harikrishnan-kp/Non_Mechanical_Anemometer/Images/Exp_setup1.jpg

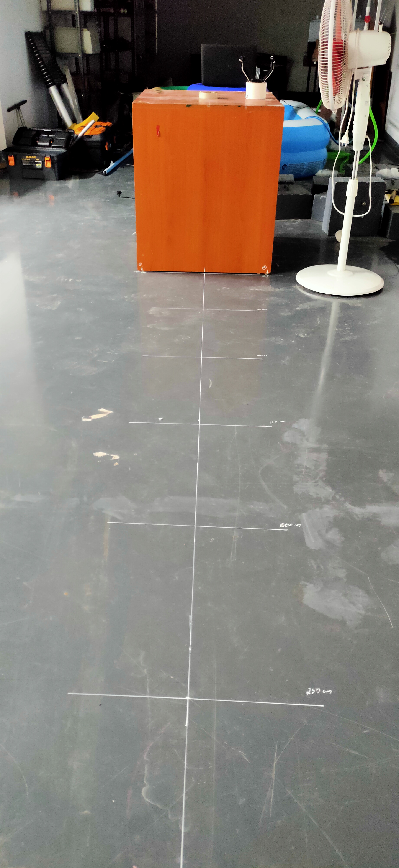
Images/Exp_setup1.jpg
