harikrishnan-kp/Non_Mechanical_Anemometer/Images/anemometer_indoor_testsetup.jpg

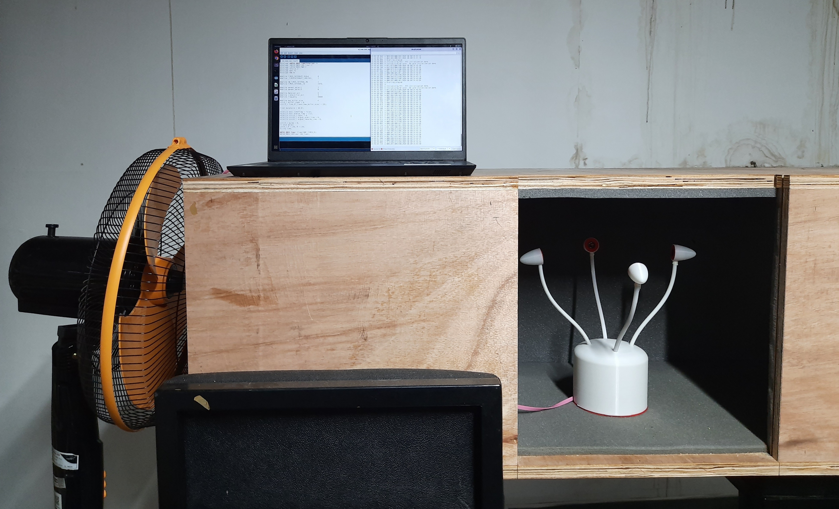
Images/anemometer_indoor_testsetup.jpg
