harikrishnan-kp/Non_Mechanical_Anemometer/Images/anemometer_result.png

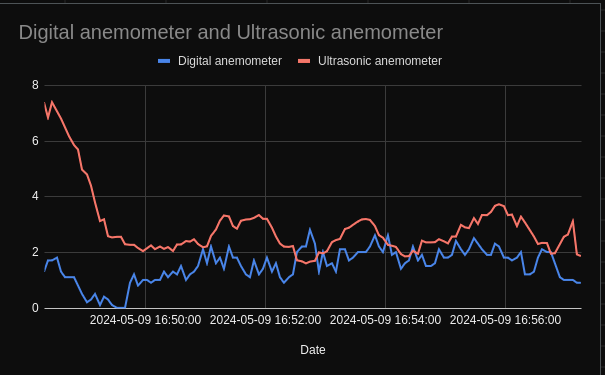
Images/anemometer_result.png
