harikrishnan-kp/Non_Mechanical_Anemometer/Design File/mux_amp_/mux_amp_.kicad_pcb

## KiCad design Blinky_6AU6/Blinky_6AU6.kicad_sch

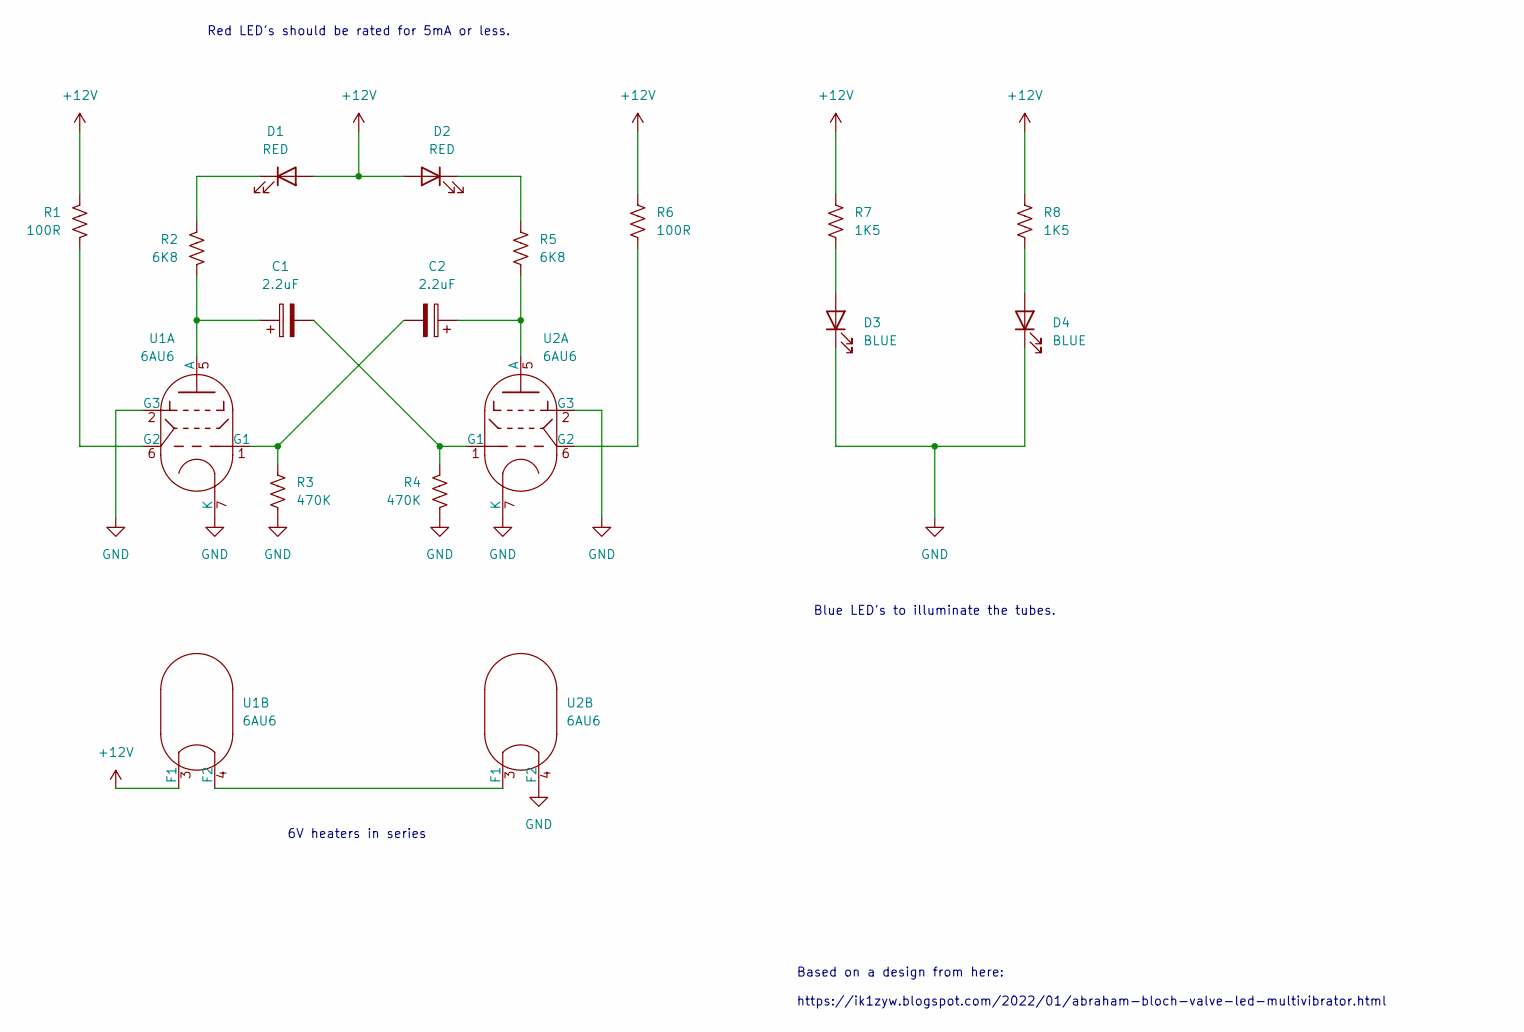
[picture p80: schematic Blinky_6AU6.kicad_sch]

Parts:
C1, C2: 2.2uF
D1, D2: RED
D3, D4: BLUE
R1, R6: 100R
R2, R5: 6K8
R3, R4: 470K
R7, R8: 1K5
U1, U2: 6AU6; Valve_Mini_P

Connections:
+12V: D1.2 (A), D2.2 (A), R1.1, R6.1, R7.1, R8.1, U1.3 (F1)
GND: D3.1 (K), D4.1 (K), R3.2, R4.2, U1.2 (G3), U1.7 (K), U2.2 (G3), U2.4 (F2), U2.7 (K)
unnamed: C1.1, R2.2, U1.5 (A)
unnamed: C1.2, R4.1, U2.1 (G1)
unnamed: C2.1, R5.2, U2.5 (A)
unnamed: C2.2, R3.1, U1.1 (G1)
unnamed: D1.1 (K), R2.1
unnamed: D2.1 (K), R5.1
unnamed: D3.2 (A), R7.2
unnamed: D4.2 (A), R8.2
unnamed: R1.2, U1.6 (G2)
unnamed: R6.2, U2.6 (G2)
unnamed: U1.4 (F2), U2.3 (F1)

Notes on the sheet:
Based on a design from here: https://ik1zyw.blogspot.com/2022/01/abraham-bloch-valve-led-multivibrator.html
Red LED's should be rated for 5mA or less.
Blue LED's to illuminate the tubes.
6V heaters in series
