harikrishnan-kp/Non_Mechanical_Anemometer/Design File/mux_amp_/mux_amp_.kicad_pcb

## KiCad design Blinky_6DJ8/Blinky_6DJ8.kicad_sch

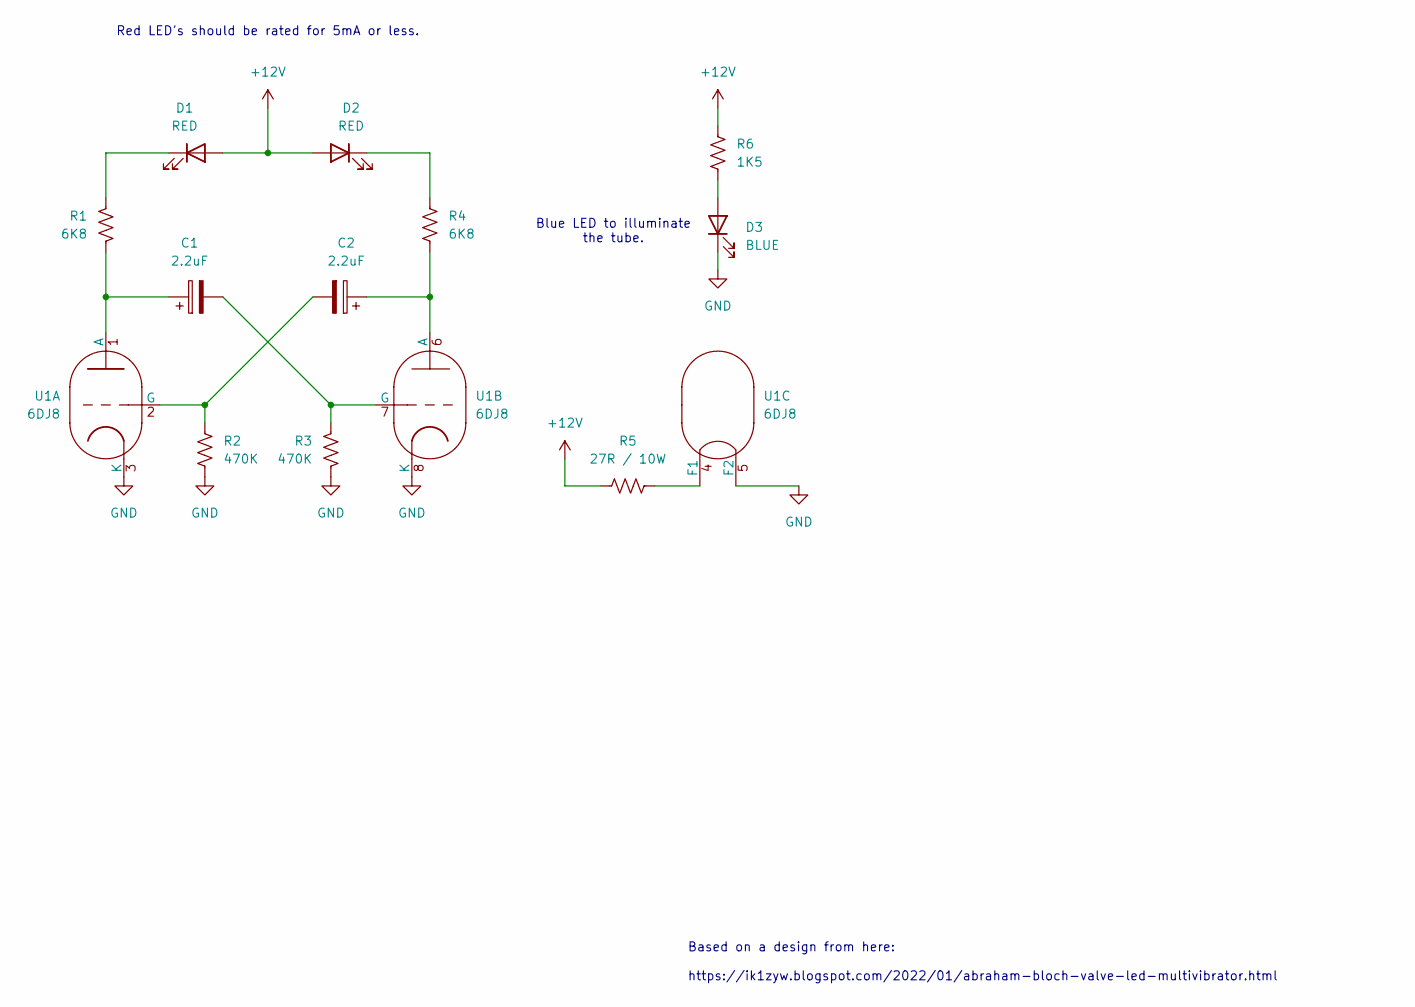
[picture p81: schematic Blinky_6DJ8.kicad_sch]

Parts:
C1, C2: 2.2uF
D1, D2: RED
D3: BLUE
R1, R4: 6K8
R2, R3: 470K
R5: 27R / 10W
R6: 1K5
U1: 6DJ8; Valve_Noval_P

Connections:
+12V: D1.2 (A), D2.2 (A), R5.1, R6.1
GND: D3.1 (K), R2.2, R3.2, U1.3 (K), U1.5 (F2), U1.8 (K)
unnamed: C1.1, R1.2, U1.1 (A)
unnamed: C1.2, R3.1, U1.7 (G)
unnamed: C2.1, R4.2, U1.6 (A)
unnamed: C2.2, R2.1, U1.2 (G)
unnamed: D1.1 (K), R1.1
unnamed: D2.1 (K), R4.1
unnamed: D3.2 (A), R6.2
unnamed: R5.2, U1.4 (F1)

Notes on the sheet:
Based on a design from here: https://ik1zyw.blogspot.com/2022/01/abraham-bloch-valve-led-multivibrator.html
Red LED's should be rated for 5mA or less.
Blue LED to illuminate the tube.
